lesitevideo/chaudiere/thermostat/pcb/thermostat_etch_silk_bottom.pdf

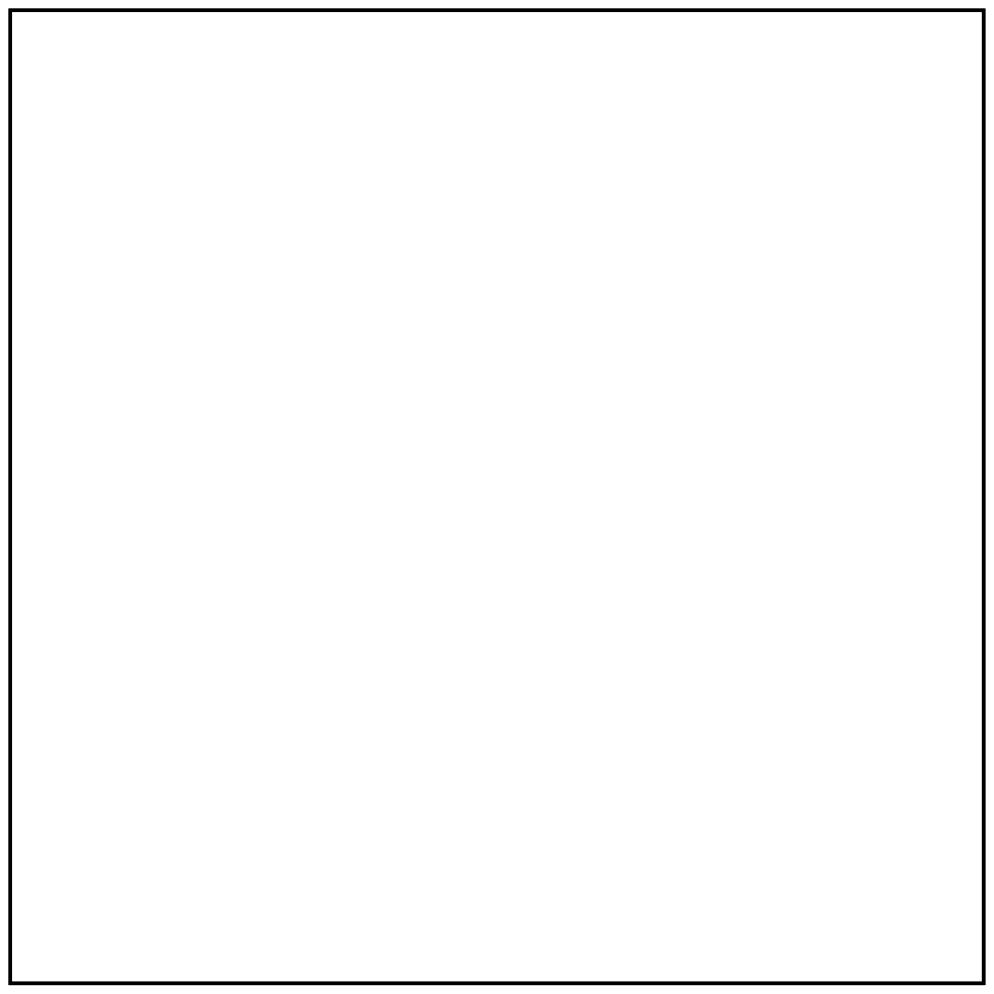
[picture p8: page 1]
