lesitevideo/chaudiere/thermostat/pcb/thermostat_etch_silk_top.pdf

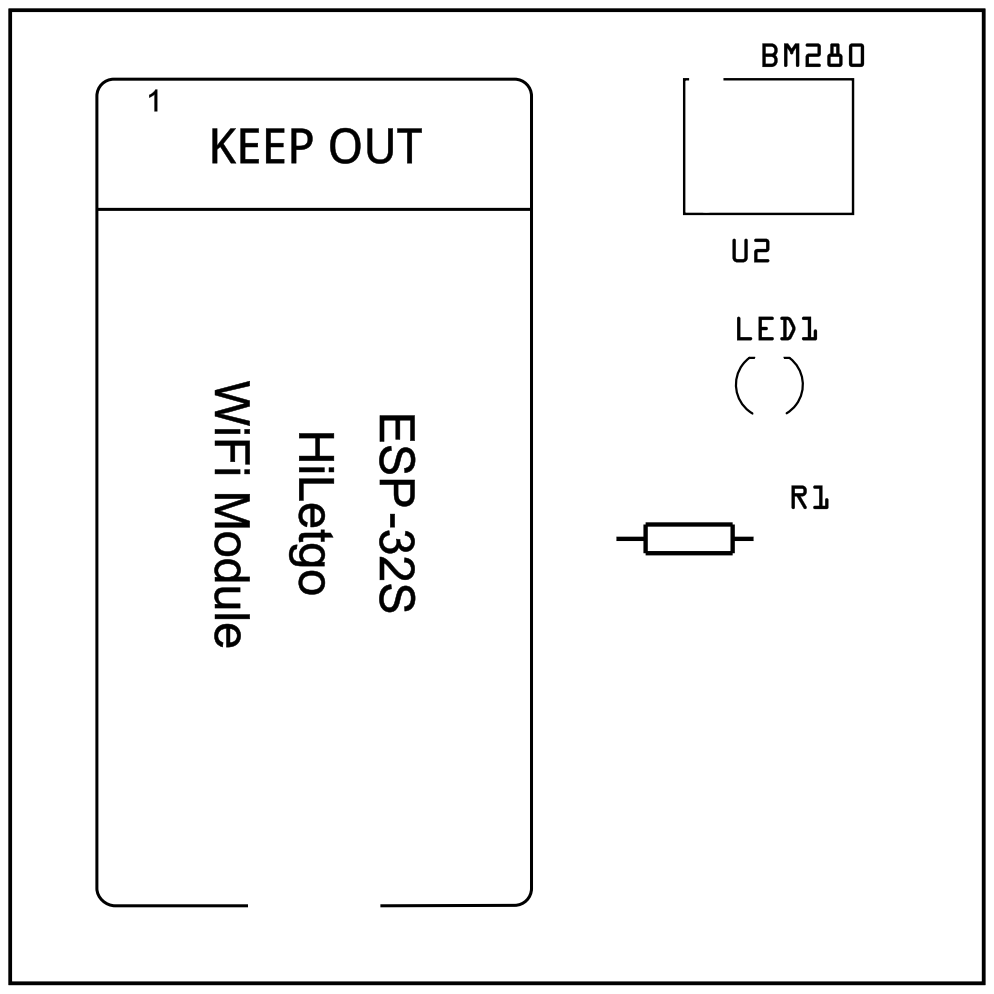
[picture p9: page 1]
