lesitevideo/chaudiere/thermostat/pcb/thermostat_etch_silk_top_mirror.pdf

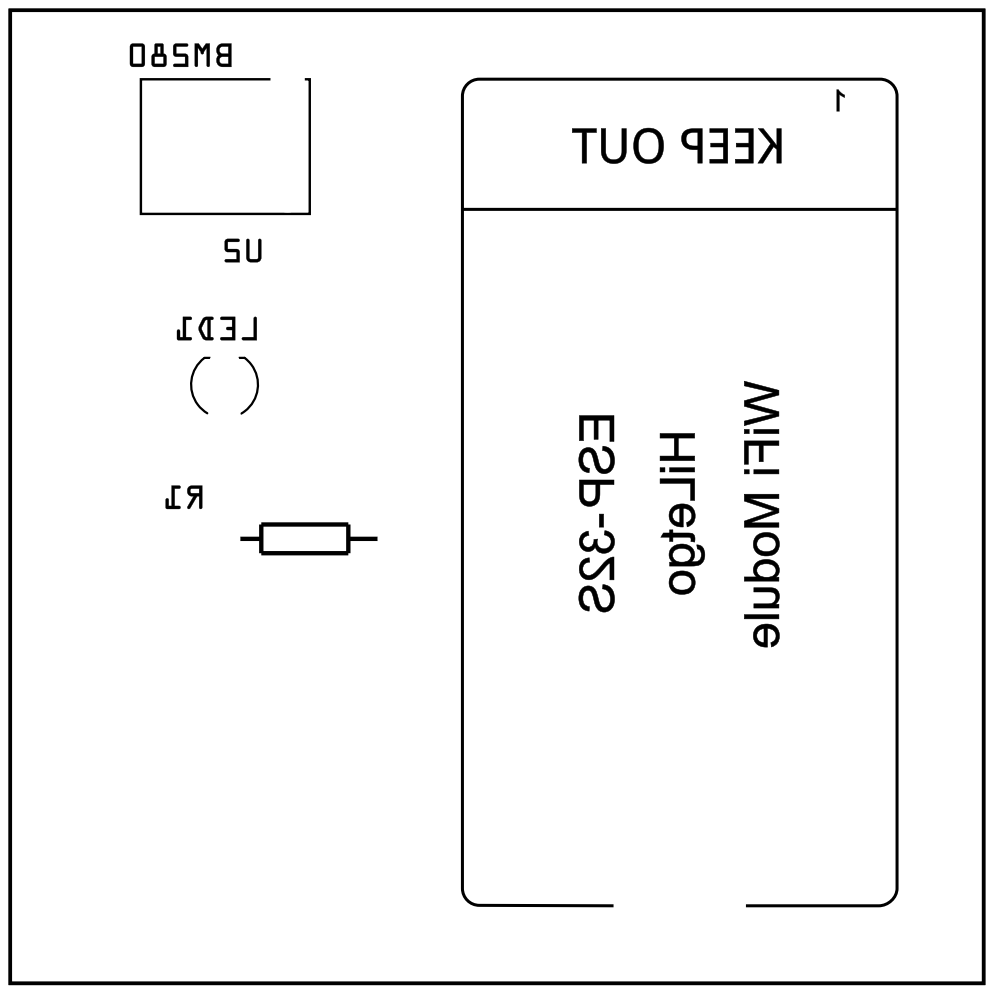
[picture p10: page 1]
